Enzo13221/SimplySplit/Images/Capture.PNG

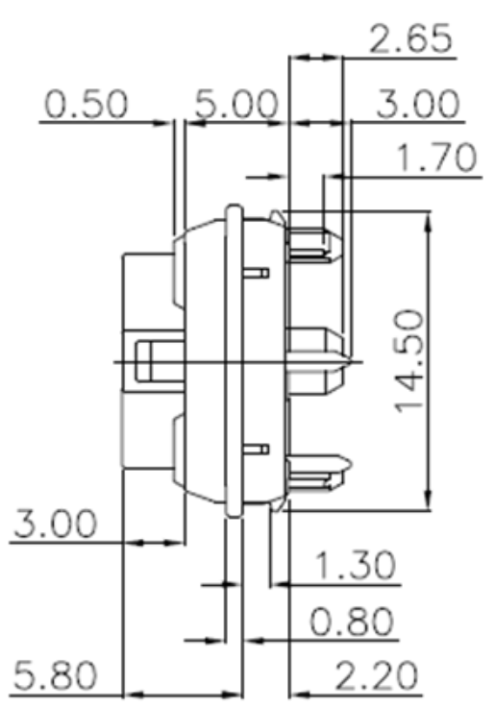
Images/Capture.PNG
