Enzo13221/SimplySplit/Images/Final.png

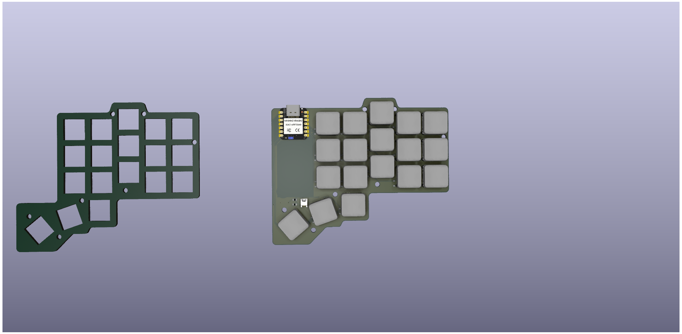
Images/Final.png
