Enzo13221/SimplySplit/Images/PCB.PNG

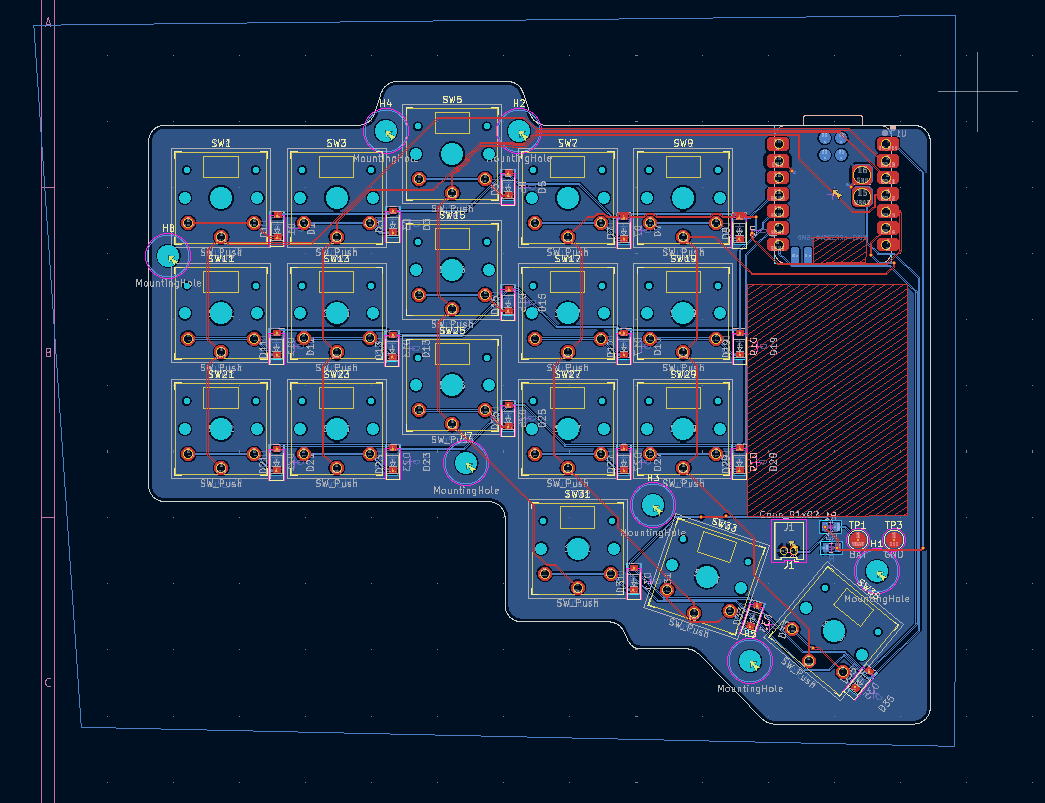
Images/PCB.PNG
