Enzo13221/SimplySplit/Images/Recipt.PNG

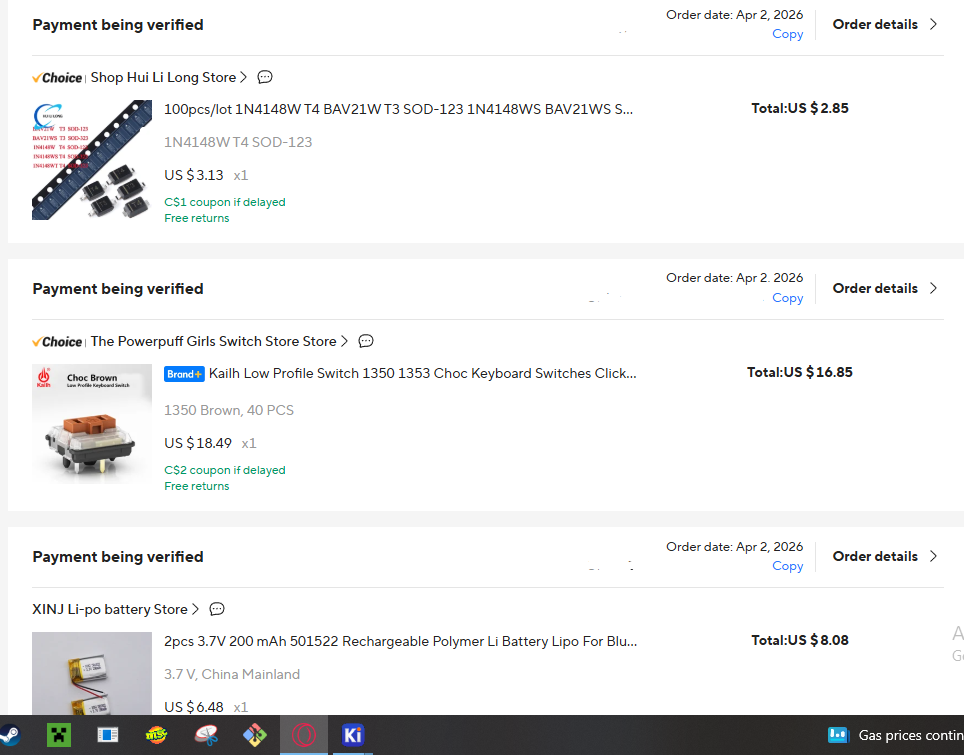
Images/Recipt.PNG
