Enzo13221/SimplySplit/Images/Simply Split8.png

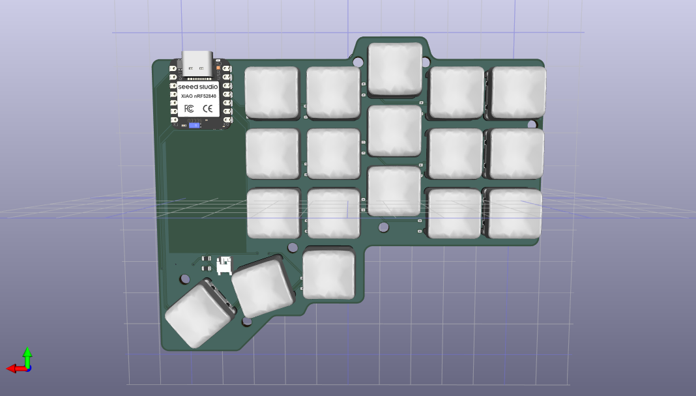
Images/Simply Split8.png
