Enzo13221/SimplySplit/Images/TopPlatePCB.PNG

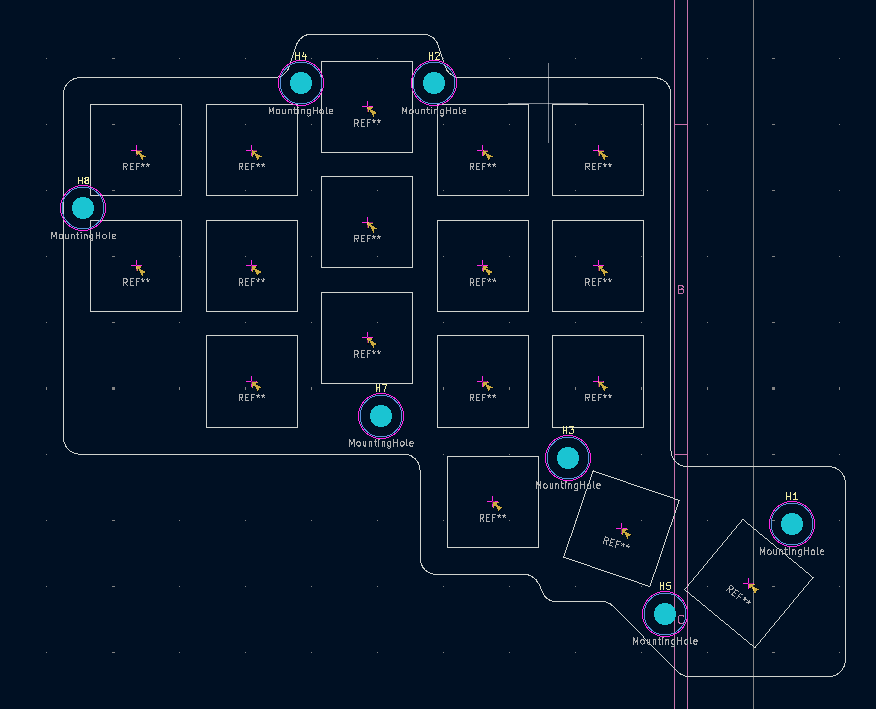
Images/TopPlatePCB.PNG
