Enzo13221/SimplySplit/Images/Cost.png

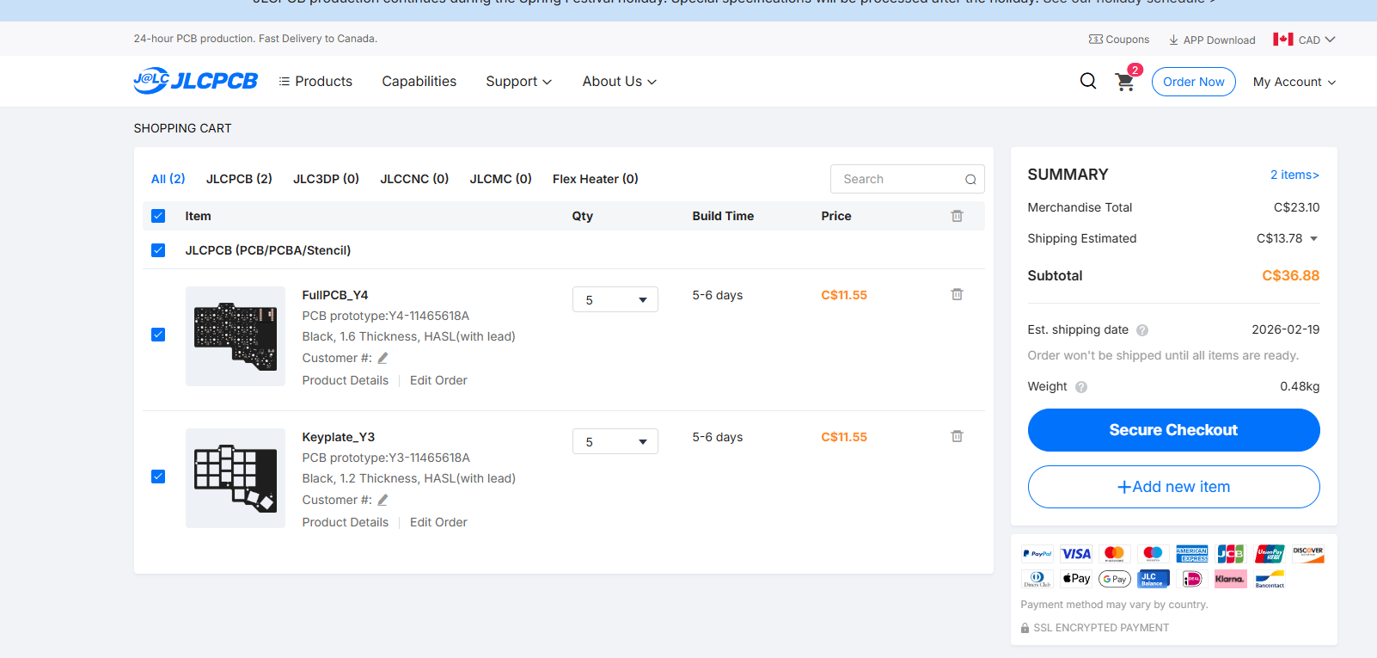
Images/Cost.png
